Studented0/PCB-Business-Card/productionold/lanyardpcbcard.pdf

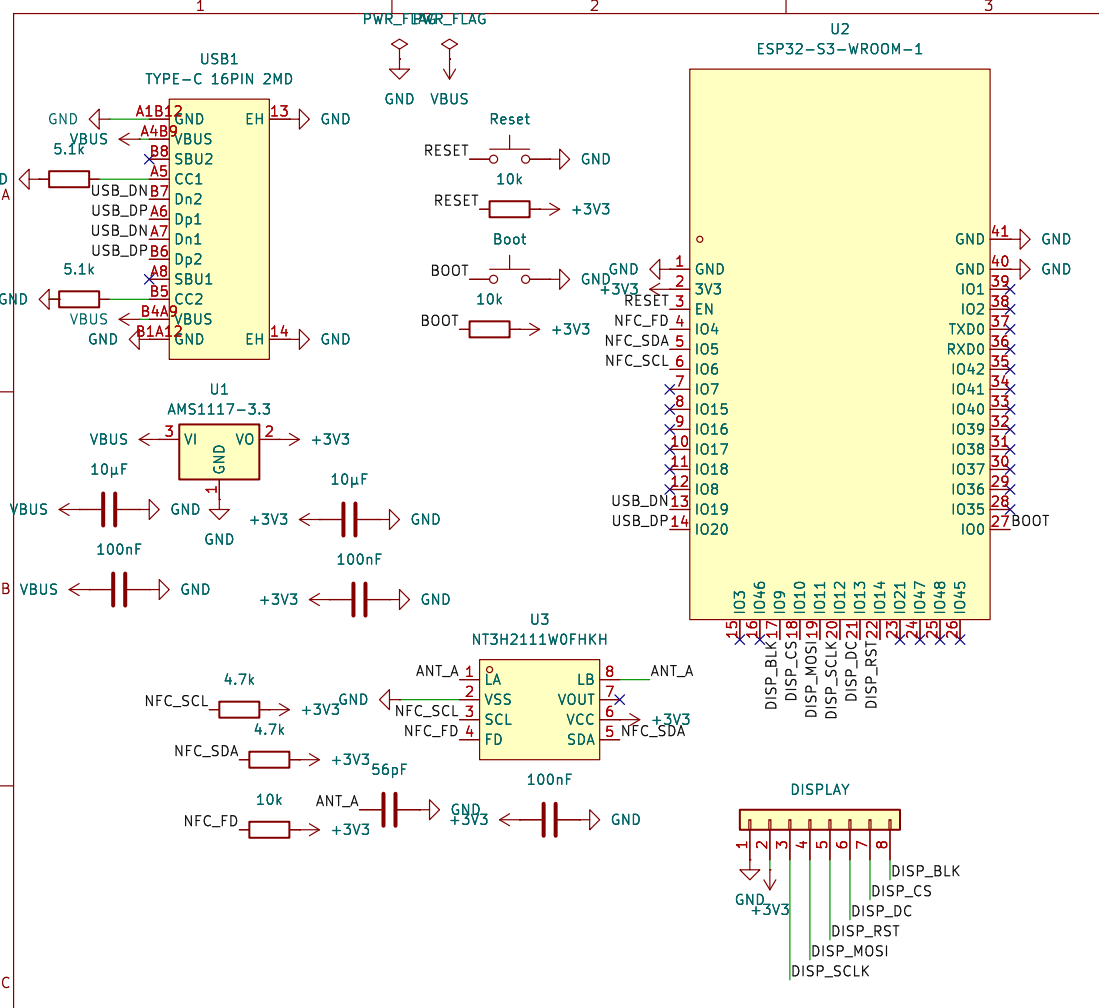
[picture p5: page 1]

Id: 1/1 Title: File: lanyardpcbcard.kicad_sch Sheet: /
