Studented0/PCB-Business-Card/productionold/lanyardpcbcard-F_Cu.pdf

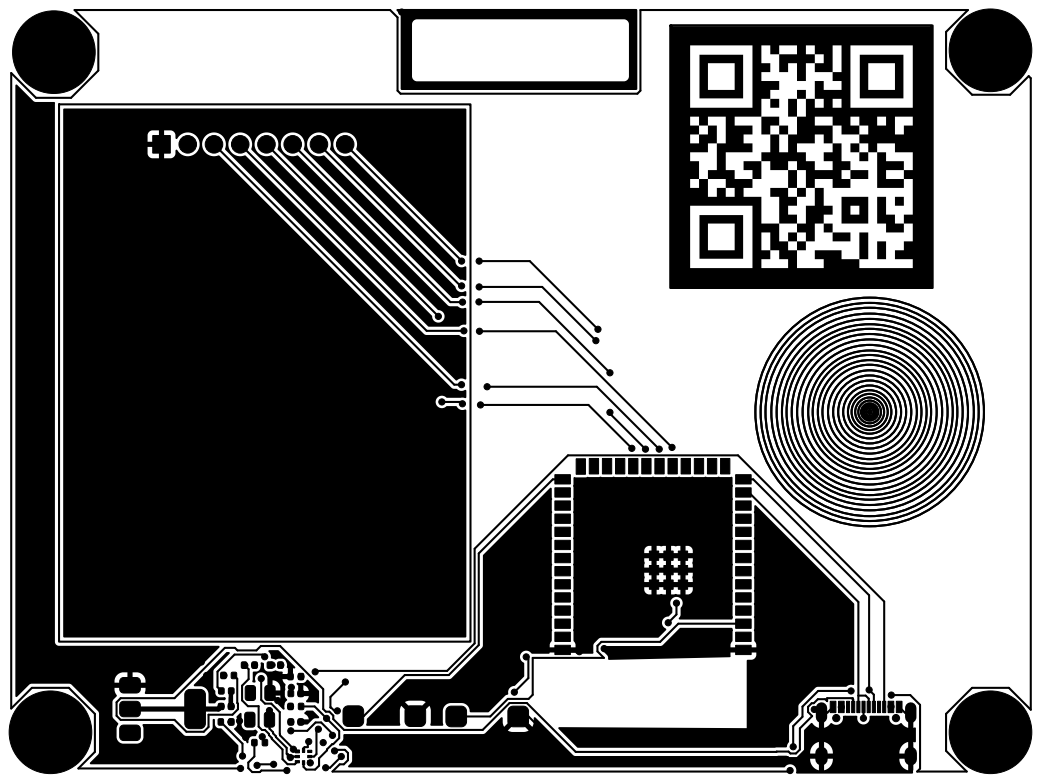
[picture p13: page 1]
