Studented0/PCB-Business-Card/productionold/lanyardpcbcard-F_Mask.pdf

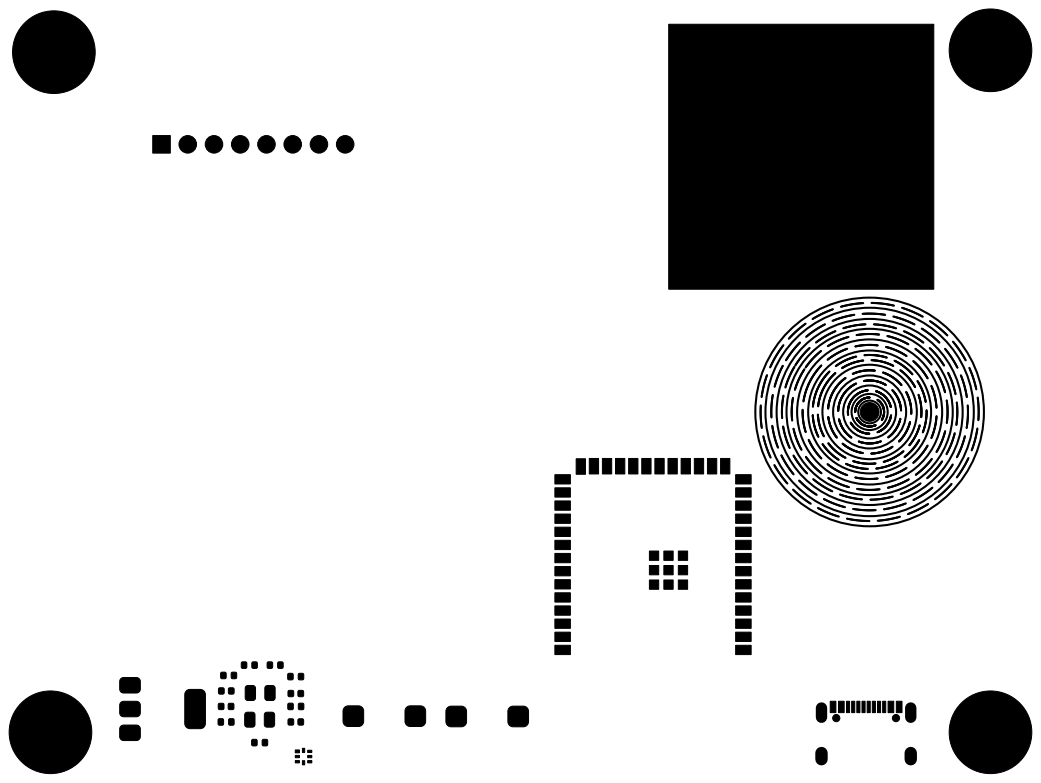
[picture p14: page 1]
