Studented0/PCB-Business-Card/productionold/lanyardpcbcard-F_Silkscreen.pdf

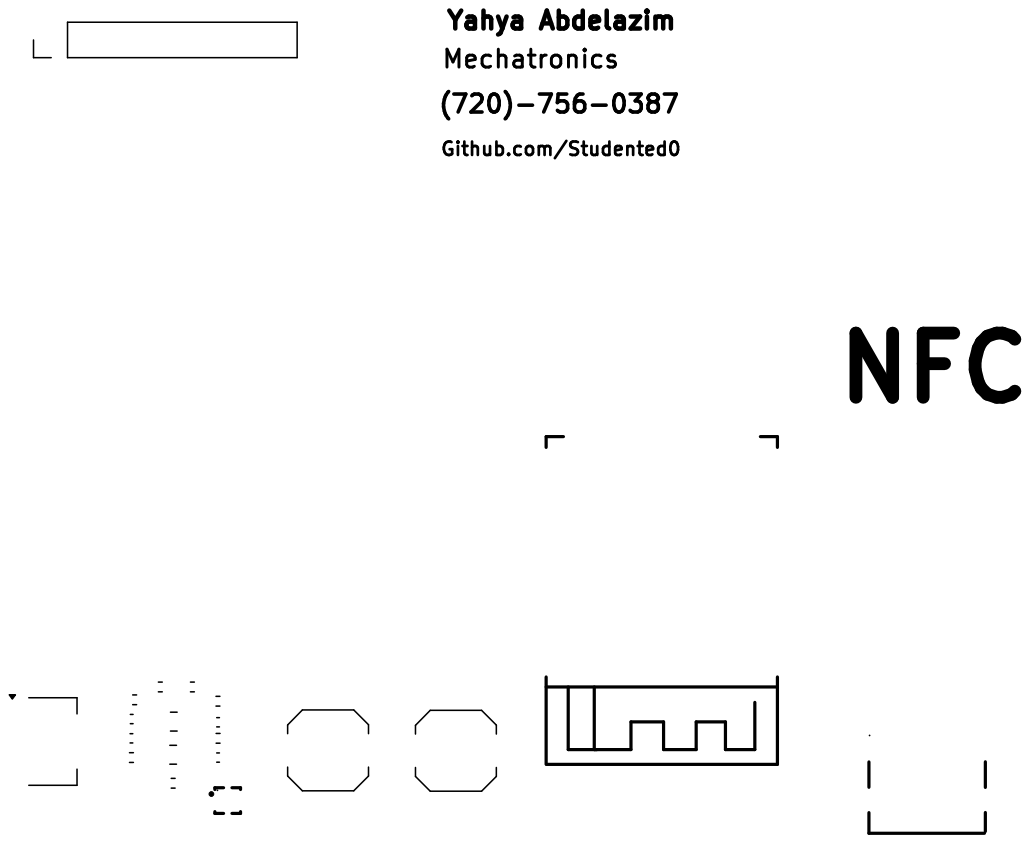
[picture p15: page 1]
